Psych0h3ad/Rapido-X/docs/cooling/validation/official_50Pa-thermal-audit.csv

patch | area_m2 | volume_out_m3_s | advected_out_W_K | diffusive_in_W_K
frontPlane | 0.00877747132036 | 8.30825382874e-05 | 4.12817301329e-08 | -4.11791803654e-06
atmosphere | 0.0422038112657 | 0.001568171221 | 0.468709495326 | -0.00400642916655
body | 0.00675752446126 | 0 | 0 | 0
hotend | 0.00344808017466 | 0 | 0 | 0
front | 0.0234139419801 | 0 | 0 | 0
rear | 0.00757623900891 | 0 | 0 | 0
fanInlet | 0.000820213378393 | -0.00165123985546 | 0 | -3.20558136107e-16
fanFrame | 0.000785593969521 | 0 | 0 | 0
heatSink | 0.00645940659354 | 0 | 0 | 0.472673224055
