Psych0h3ad/Rapido-X/docs/cooling/validation/p3d_10Pa-thermal-audit.csv

patch | area_m2 | volume_out_m3_s | advected_out_W_K | diffusive_in_W_K
frontPlane | 0.00877788598332 | 8.55633272496e-05 | 0.000315778788734 | -0.000277857834102
atmosphere | 0.0422038112657 | 0.00054568145512 | 0.316810668245 | -0.00583837345382
body | 0.00676604357792 | 0 | 0 | 0
hotend | 0.00348356291914 | 0 | 0 | 0
front | 0.0228788535844 | 0 | 0 | 0
rear | 0.00773710371151 | 0 | 0 | 0
fanInlet | 0.000819975238582 | -0.000631281833705 | 0 | -2.78098443329e-23
fanFrame | 0.000785876039656 | 0 | 0 | 0
heatSink | 0.00732671841479 | 0 | 0 | 0.323280053083
