Psych0h3ad/Rapido-X/docs/cooling/validation/p3d_25Pa-thermal-audit.csv

patch | area_m2 | volume_out_m3_s | advected_out_W_K | diffusive_in_W_K
frontPlane | 0.00877788598332 | 0.000165018108336 | 0.00216322585746 | -0.000353572722087
atmosphere | 0.0422038112657 | 0.000923908488958 | 0.458119784613 | -0.00593501832953
body | 0.00676604357792 | 0 | 0 | 0
hotend | 0.00348356291914 | 0 | 0 | 0
front | 0.0228788535844 | 0 | 0 | 0
rear | 0.00773710371151 | 0 | 0 | 0
fanInlet | 0.000819975238582 | -0.00108892314808 | 0 | -3.04016445743e-29
fanFrame | 0.000785876039656 | 0 | 0 | 0
heatSink | 0.00732671841479 | 0 | 0 | 0.466565811853
