Psych0h3ad/Rapido-X/docs/cooling/validation/p3d_50Pa-thermal-audit.csv

patch | area_m2 | volume_out_m3_s | advected_out_W_K | diffusive_in_W_K
frontPlane | 0.00877788598332 | 0.000260675241426 | 0.00456209706449 | -0.000584690430038
atmosphere | 0.0422038112657 | 0.00135993695877 | 0.584953905972 | -0.00738390831647
body | 0.00676604357792 | 0 | 0 | 0
hotend | 0.00348356291914 | 0 | 0 | 0
front | 0.0228788535844 | 0 | 0 | 0
rear | 0.00773710371151 | 0 | 0 | 0
fanInlet | 0.000819975238582 | -0.00162065769624 | 0 | -7.13004020155e-32
fanFrame | 0.000785876039656 | 0 | 0 | 0
heatSink | 0.00732671841479 | 0 | 0 | 0.59754699048
